goallight/gun-stands/builds/sig_p365x/sig_p365x_fit_test.stl

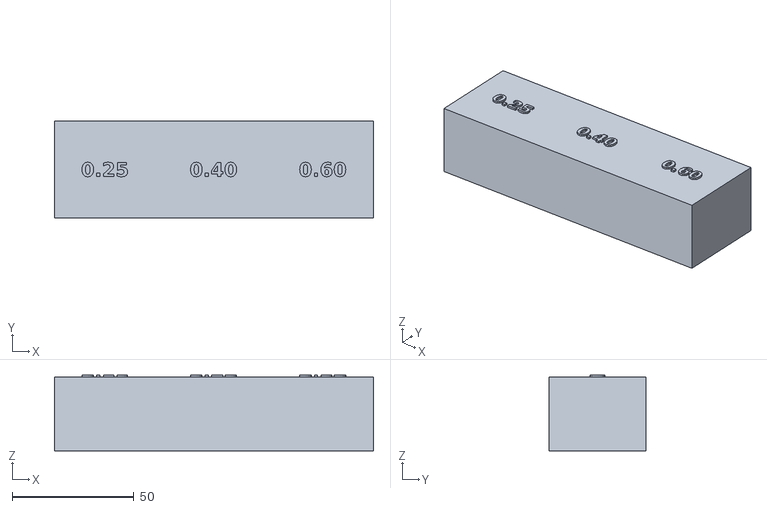
[picture p15: CAD file, 2026-08-14]
builds/sig_p365x/sig_p365x_fit_test.stl
131.2 x 40.0 x 31.1
